kevinr94/Proyecto-Mecatronica-Bogado-Roges/Contenido multimedia/Imagen de WhatsApp 2025-07-23 a las 09.27.17_4d64eca1.jpg

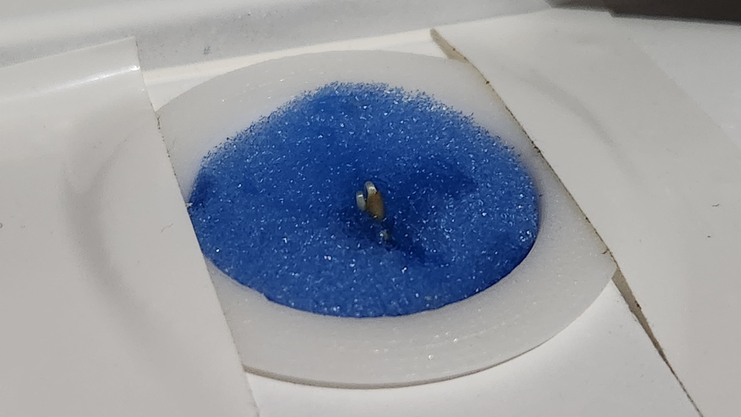
Contenido multimedia/Imagen de WhatsApp 2025-07-23 a las 09.27.17_4d64eca1.jpg
