kevinr94/Proyecto-Mecatronica-Bogado-Roges/Contenido multimedia/Imagen de WhatsApp 2025-07-23 a las 09.27.26_3c1b3ca0.jpg

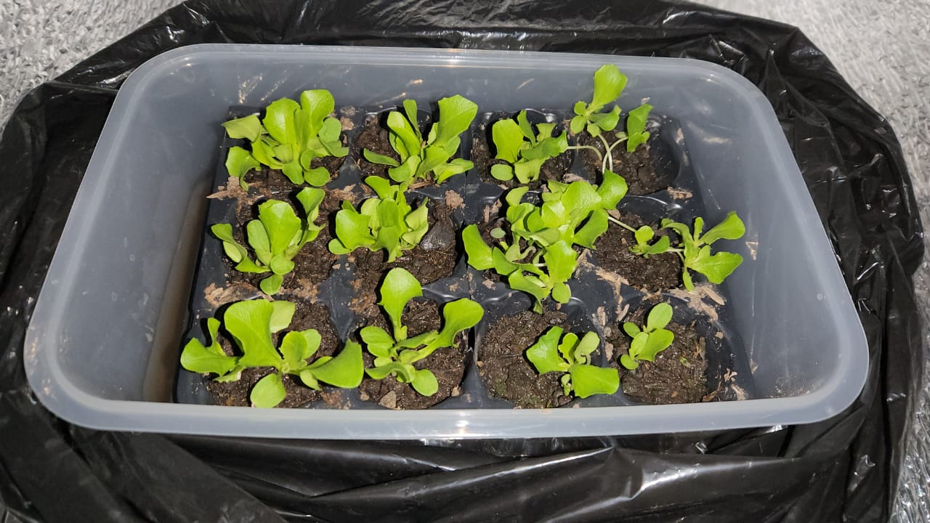
Contenido multimedia/Imagen de WhatsApp 2025-07-23 a las 09.27.26_3c1b3ca0.jpg
