kevinr94/Proyecto-Mecatronica-Bogado-Roges/Contenido multimedia/IMG-20250506-WA0042.jpg

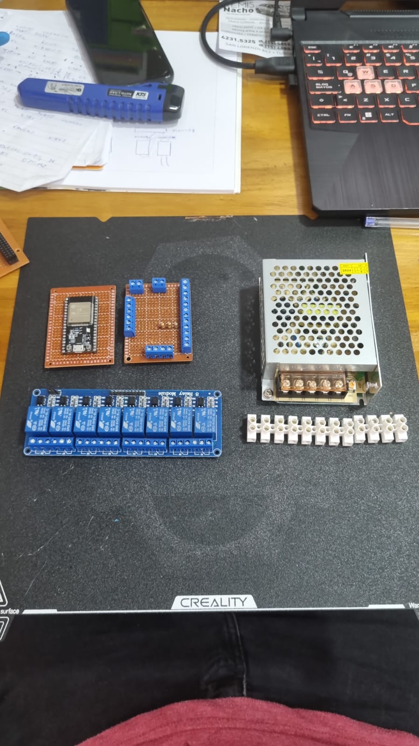
Contenido multimedia/IMG-20250506-WA0042.jpg
