kevinr94/Proyecto-Mecatronica-Bogado-Roges/Contenido multimedia/IMG-20250507-WA0024.jpg

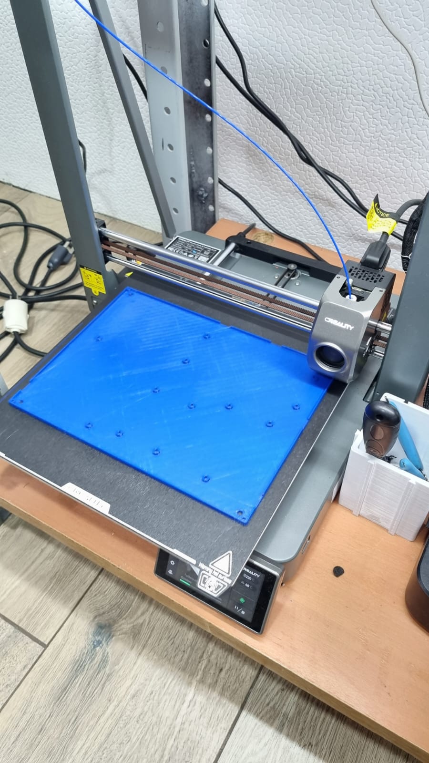
Contenido multimedia/IMG-20250507-WA0024.jpg
