kevinr94/Proyecto-Mecatronica-Bogado-Roges/Contenido multimedia/IMG-20250508-WA0039.jpg

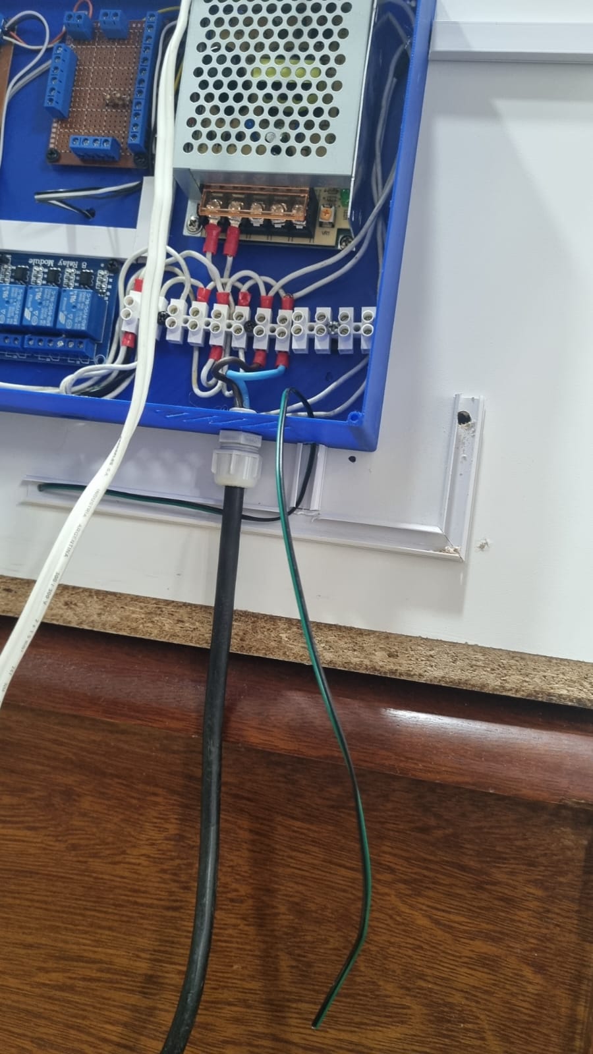
Contenido multimedia/IMG-20250508-WA0039.jpg
