kevinr94/Proyecto-Mecatronica-Bogado-Roges/Contenido multimedia/IMG-20250515-WA0036.jpg

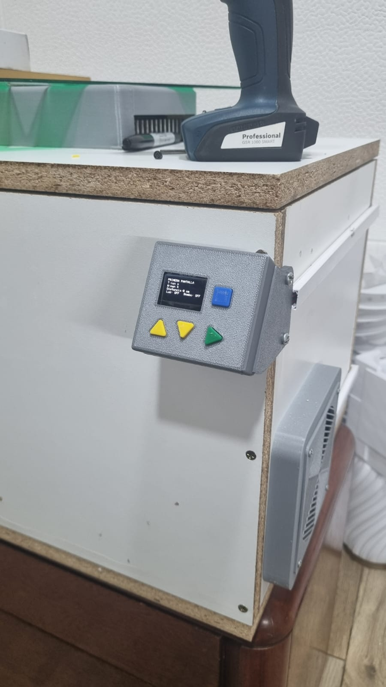
Contenido multimedia/IMG-20250515-WA0036.jpg
