kevinr94/Proyecto-Mecatronica-Bogado-Roges/Contenido multimedia/IMG-20250519-WA0019.jpg

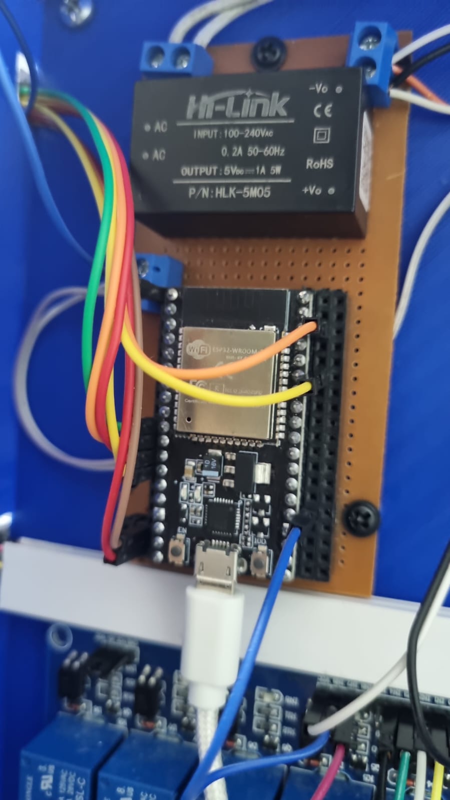
Contenido multimedia/IMG-20250519-WA0019.jpg
