kevinr94/Proyecto-Mecatronica-Bogado-Roges/Contenido multimedia/IMG-20250530-WA0029.jpg

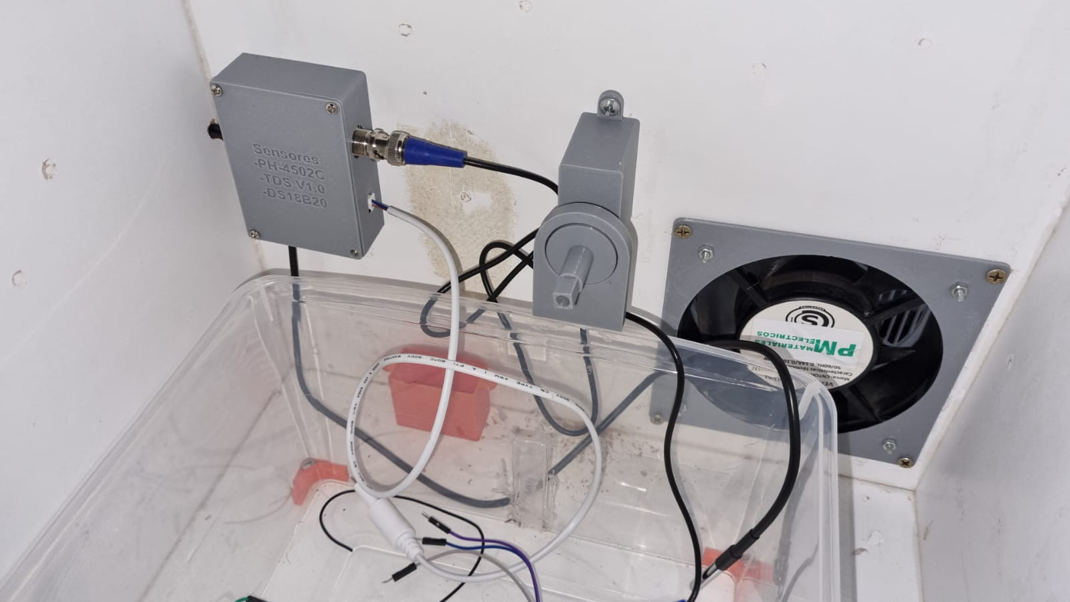
Contenido multimedia/IMG-20250530-WA0029.jpg
