kevinr94/Proyecto-Mecatronica-Bogado-Roges/Contenido multimedia/IMG-20250604-WA0013.jpg

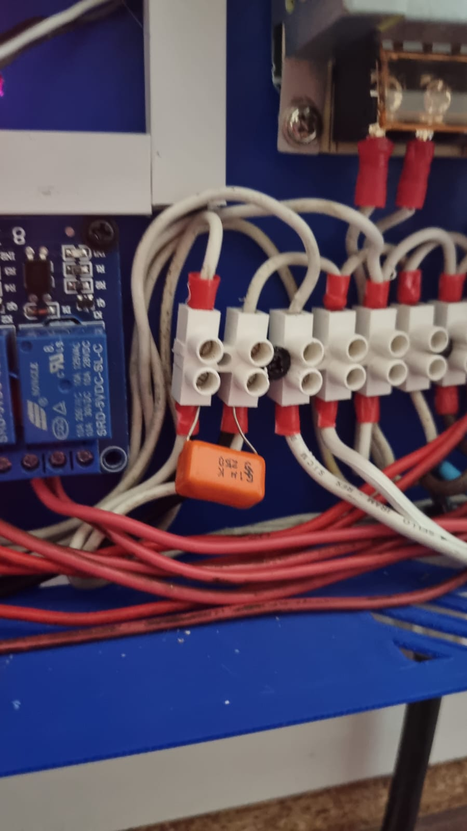
Contenido multimedia/IMG-20250604-WA0013.jpg
