kevinr94/Proyecto-Mecatronica-Bogado-Roges/Contenido multimedia/IMG-20250610-WA0012.jpg

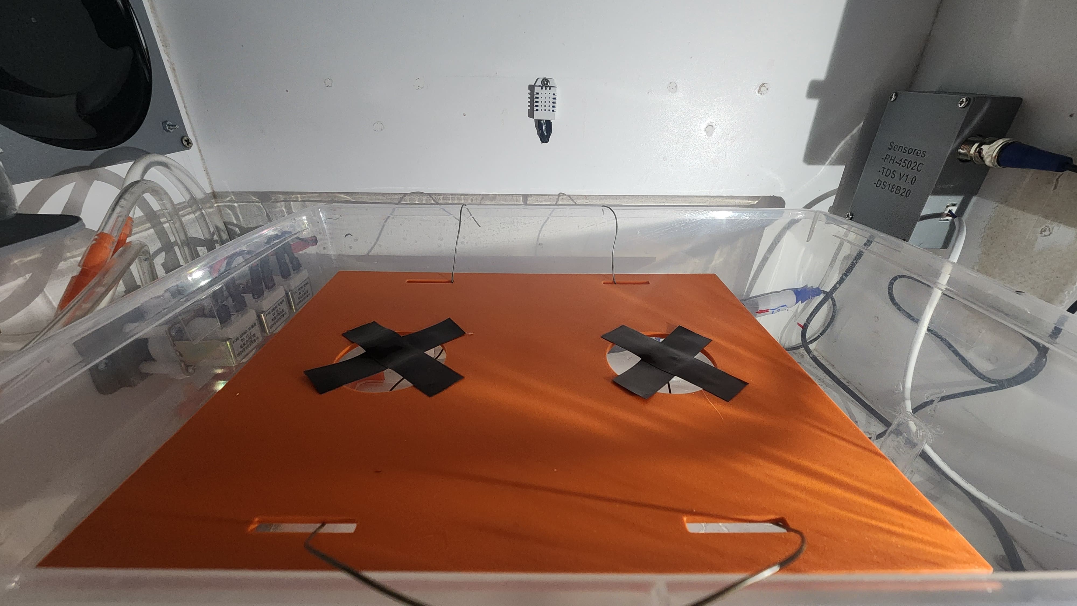
Contenido multimedia/IMG-20250610-WA0012.jpg
