kevinr94/Proyecto-Mecatronica-Bogado-Roges/Contenido multimedia/IMG-20250617-WA0007.jpg

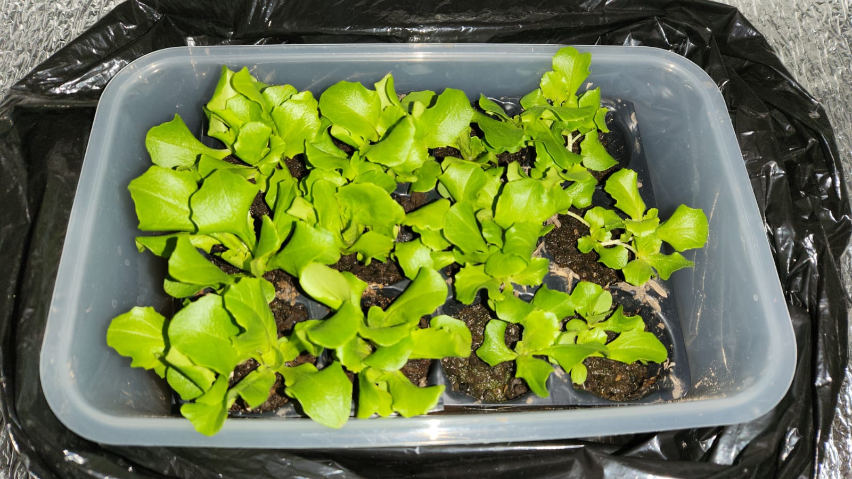
Contenido multimedia/IMG-20250617-WA0007.jpg
