kevinr94/Proyecto-Mecatronica-Bogado-Roges/Contenido multimedia/IMG-20250618-WA0008.jpg

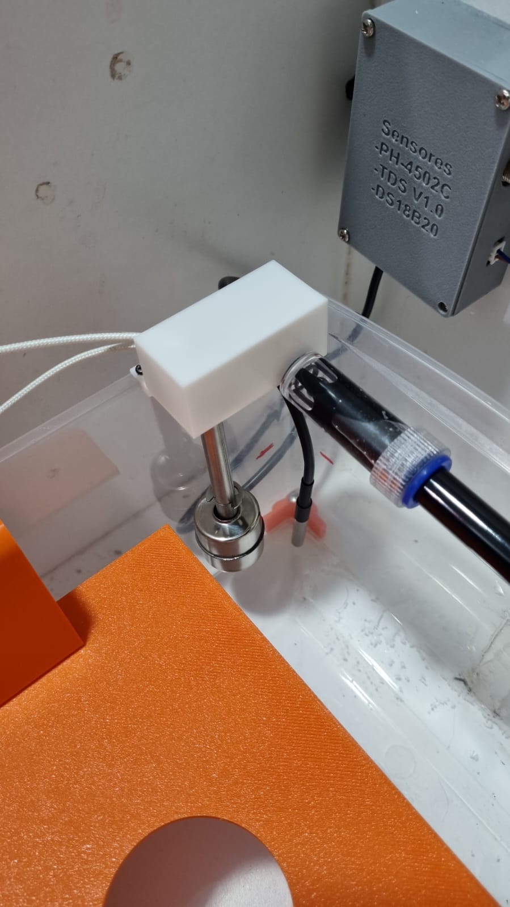
Contenido multimedia/IMG-20250618-WA0008.jpg
