kevinr94/Proyecto-Mecatronica-Bogado-Roges/Contenido multimedia/IMG-20250624-WA0001.jpg

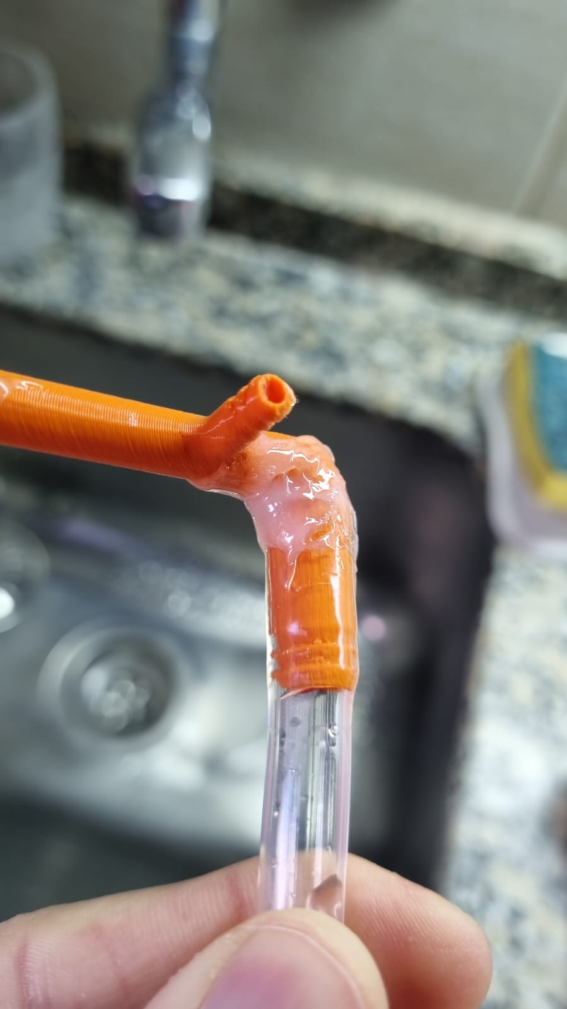
Contenido multimedia/IMG-20250624-WA0001.jpg
