kevinr94/Proyecto-Mecatronica-Bogado-Roges/Contenido multimedia/IMG-20250625-WA0002.jpg

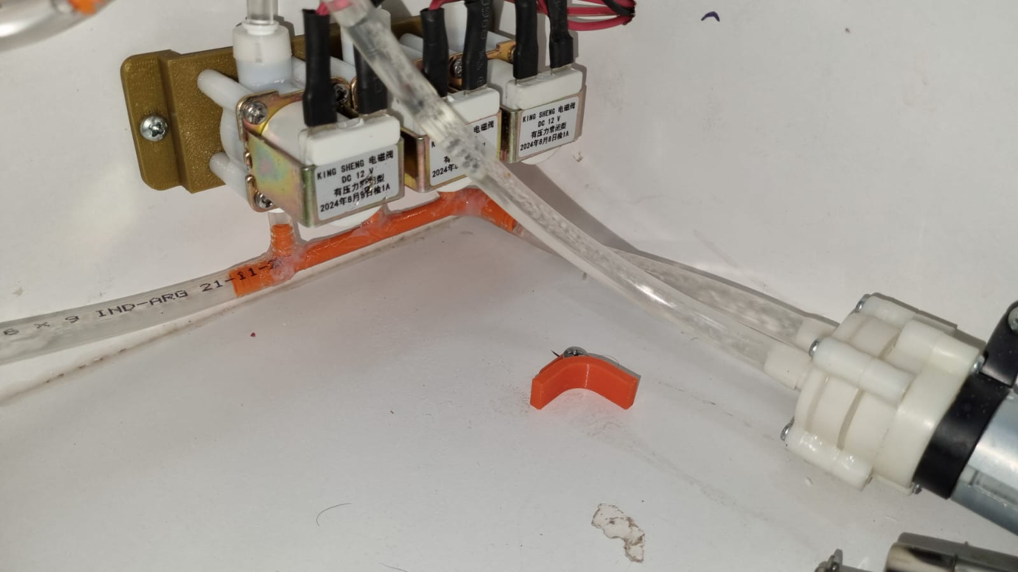
Contenido multimedia/IMG-20250625-WA0002.jpg
