kevinr94/Proyecto-Mecatronica-Bogado-Roges/Contenido multimedia/IMG-20250630-WA0049.jpg

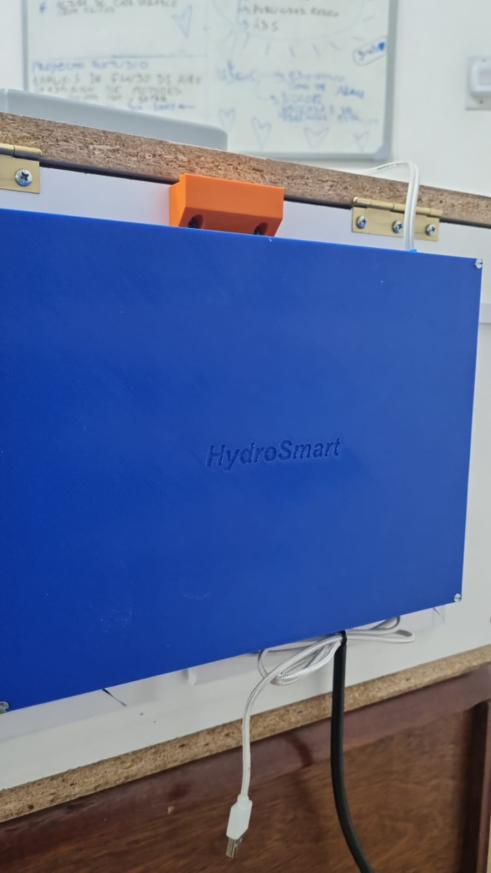
Contenido multimedia/IMG-20250630-WA0049.jpg
