kevinr94/Proyecto-Mecatronica-Bogado-Roges/Contenido multimedia/IMG-20250723-WA0024.jpg

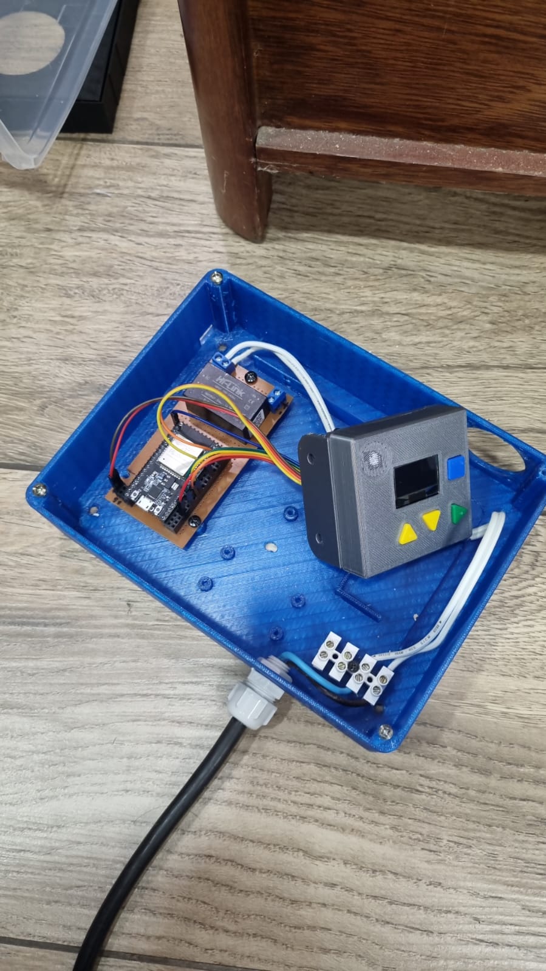
Contenido multimedia/IMG-20250723-WA0024.jpg
