kevinr94/Proyecto-Mecatronica-Bogado-Roges/Contenido multimedia/IMG-20250723-WA0030.jpg

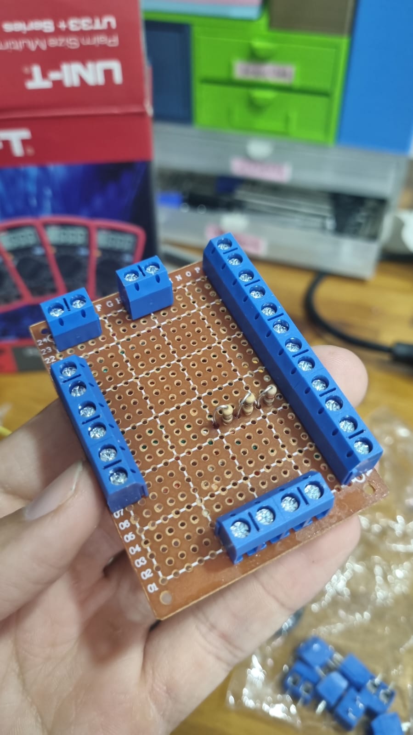
Contenido multimedia/IMG-20250723-WA0030.jpg
