kevinr94/Proyecto-Mecatronica-Bogado-Roges/Archivos 3D para imprimir/Raccord para EV chico.stl

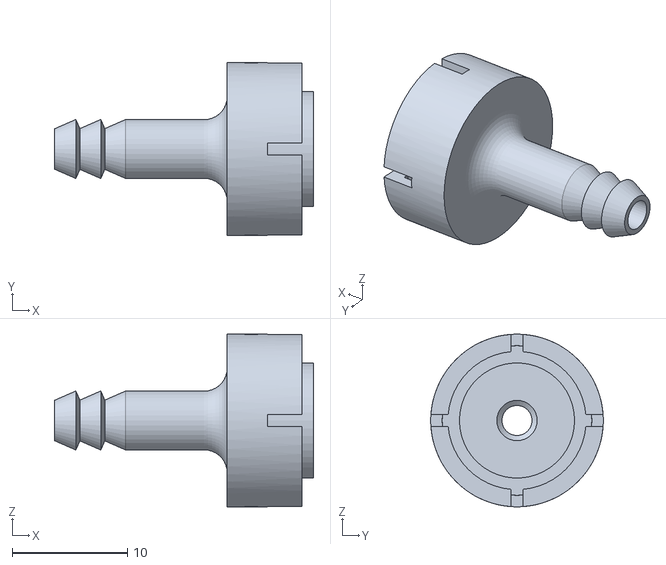
[picture p100: CAD file, 2025-07-23]
Archivos 3D para imprimir/Raccord para EV chico.stl
22.5 x 15.0 x 15.0
