kevinr94/Proyecto-Mecatronica-Bogado-Roges/Archivos 3D para imprimir/Protector iluminacion.stl

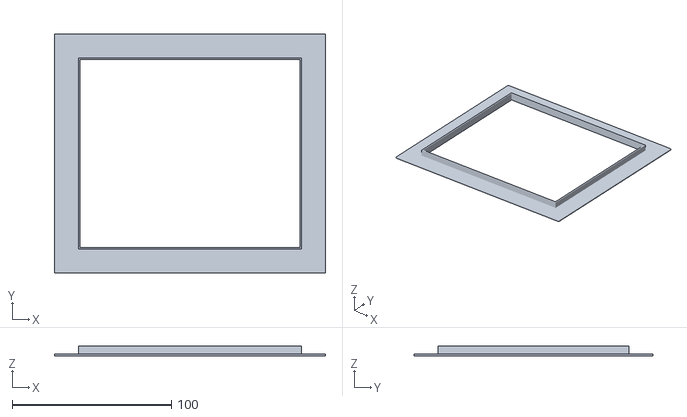
[picture p101: CAD file, 2025-07-23]
Archivos 3D para imprimir/Protector iluminacion.stl
170.0 x 150.0 x 6.00
