kevinr94/Proyecto-Mecatronica-Bogado-Roges/Archivos 3D para imprimir/Soporte electroválvulas.stl

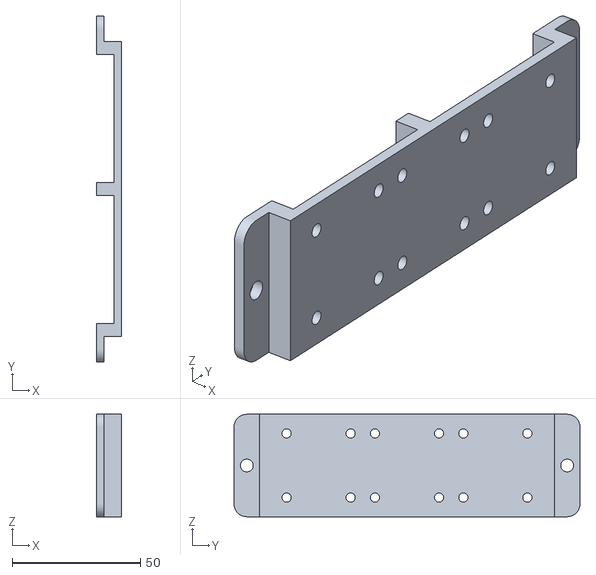
[picture p102: CAD file, 2025-07-23]
Archivos 3D para imprimir/Soporte electroválvulas.stl
9.79 x 135.0 x 40.0
