kevinr94/Proyecto-Mecatronica-Bogado-Roges/Archivos 3D para imprimir/Soporte ultrasonido.stl

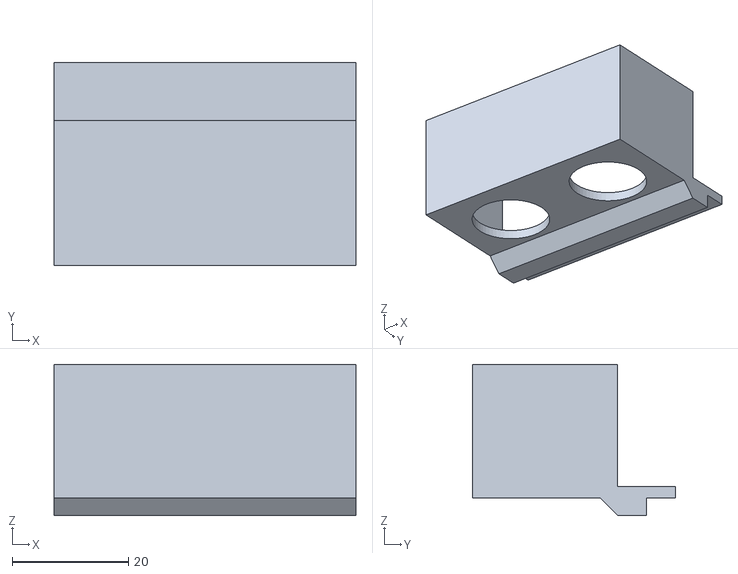
[picture p103: CAD file, 2025-07-23]
Archivos 3D para imprimir/Soporte ultrasonido.stl
52.0 x 35.0 x 26.0
