kevinr94/Proyecto-Mecatronica-Bogado-Roges/Archivos 3D para imprimir/Soporte trasero cooler.stl

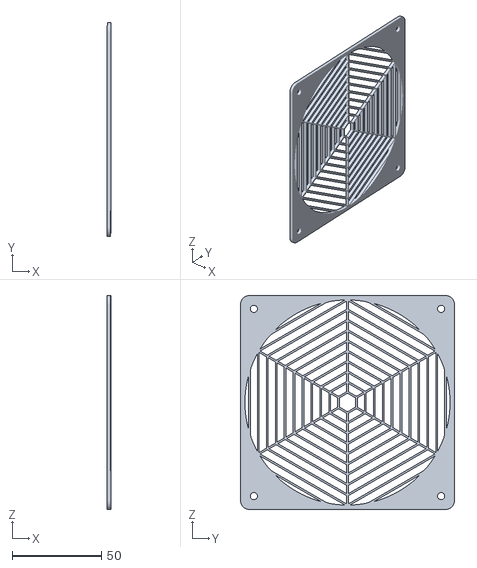
[picture p104: CAD file, 2025-07-23]
Archivos 3D para imprimir/Soporte trasero cooler.stl
2.05 x 120.0 x 120.0
