kevinr94/Proyecto-Mecatronica-Bogado-Roges/Archivos 3D para imprimir/Soporte servomotor.stl

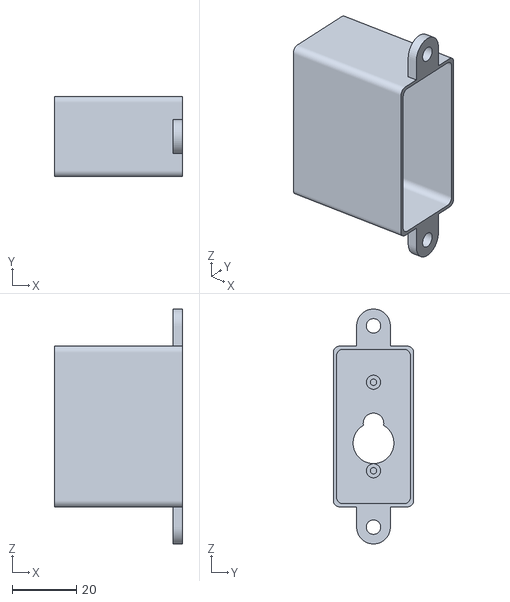
[picture p105: CAD file, 2025-07-23]
Archivos 3D para imprimir/Soporte servomotor.stl
39.9 x 25.0 x 73.1
