kevinr94/Proyecto-Mecatronica-Bogado-Roges/Archivos 3D para imprimir/Soporte fan iluminacion.stl

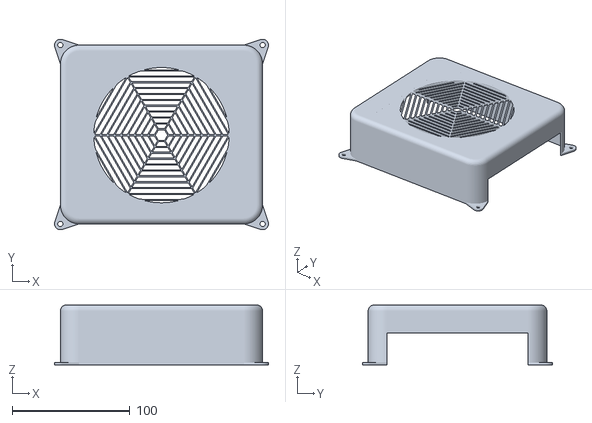
[picture p106: CAD file, 2025-07-23]
Archivos 3D para imprimir/Soporte fan iluminacion.stl
182.0 x 162.0 x 51.0
