kevinr94/Proyecto-Mecatronica-Bogado-Roges/Archivos 3D para imprimir/Tablero electrico.stl

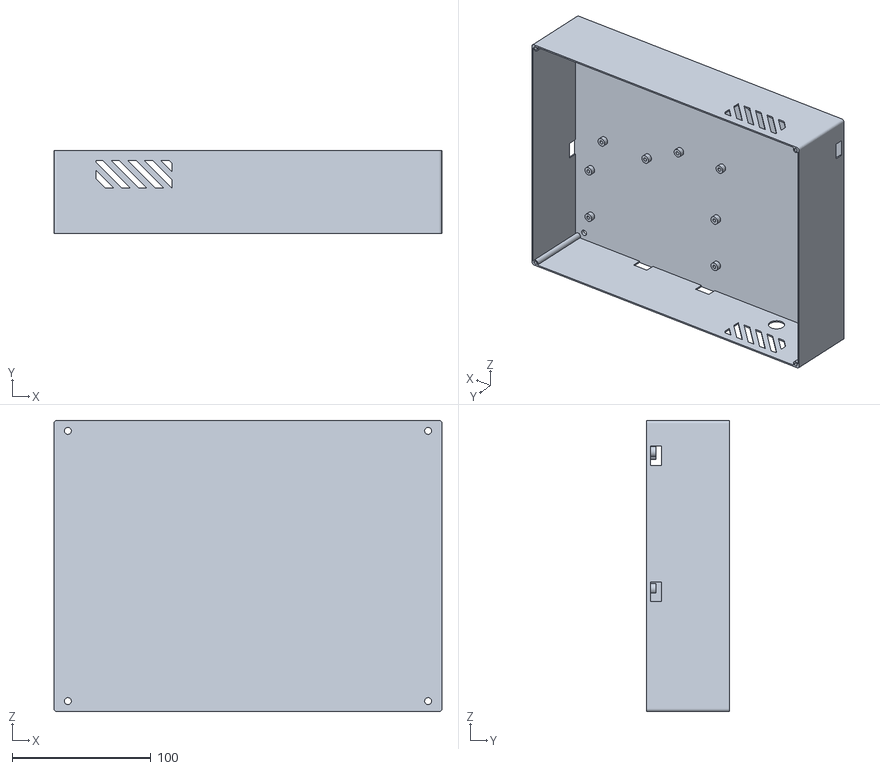
[picture p107: CAD file, 2025-07-23]
Archivos 3D para imprimir/Tablero electrico.stl
280.0 x 60.0 x 210.0
