kevinr94/Proyecto-Mecatronica-Bogado-Roges/Archivos 3D para imprimir/Carcasa base.stl

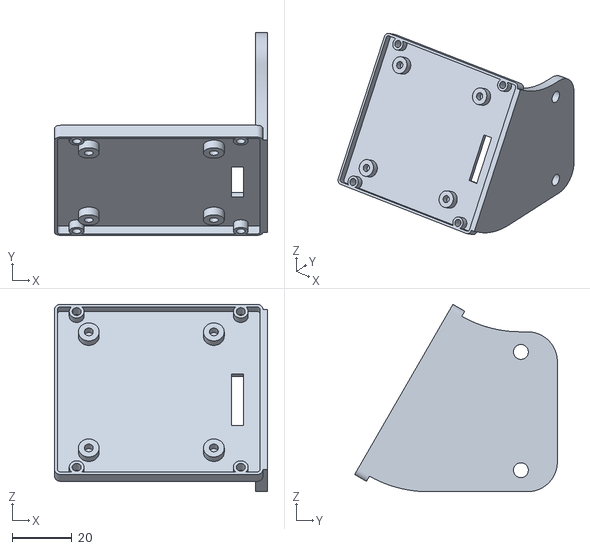
[picture p108: CAD file, 2025-07-23]
Archivos 3D para imprimir/Carcasa base.stl
71.5 x 68.1 x 62.9
