kevinr94/Proyecto-Mecatronica-Bogado-Roges/Archivos 3D para imprimir/Reparacion EV.stl

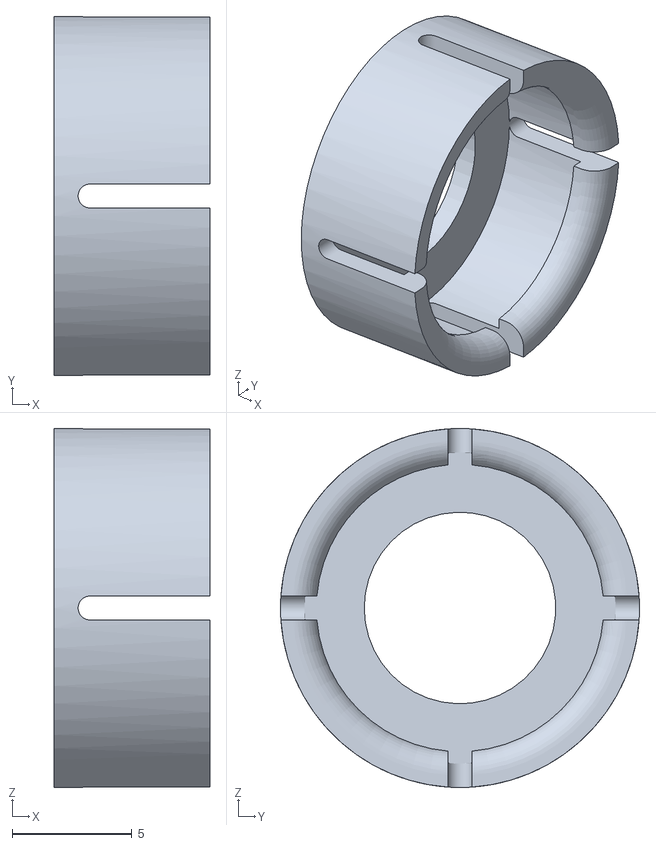
[picture p109: CAD file, 2025-07-23]
Archivos 3D para imprimir/Reparacion EV.stl
6.50 x 15.0 x 15.0
