kevinr94/Proyecto-Mecatronica-Bogado-Roges/Archivos 3D para imprimir/racor.stl

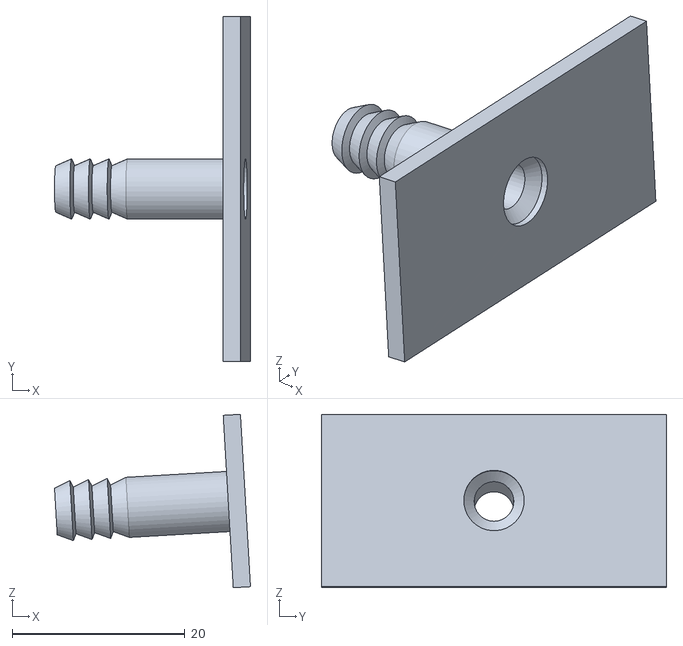
[picture p110: CAD file, 2025-07-23]
Archivos 3D para imprimir/racor.stl
22.7 x 40.0 x 20.1
