kevinr94/Proyecto-Mecatronica-Bogado-Roges/Archivos 3D para imprimir/Soportes sensore.stl

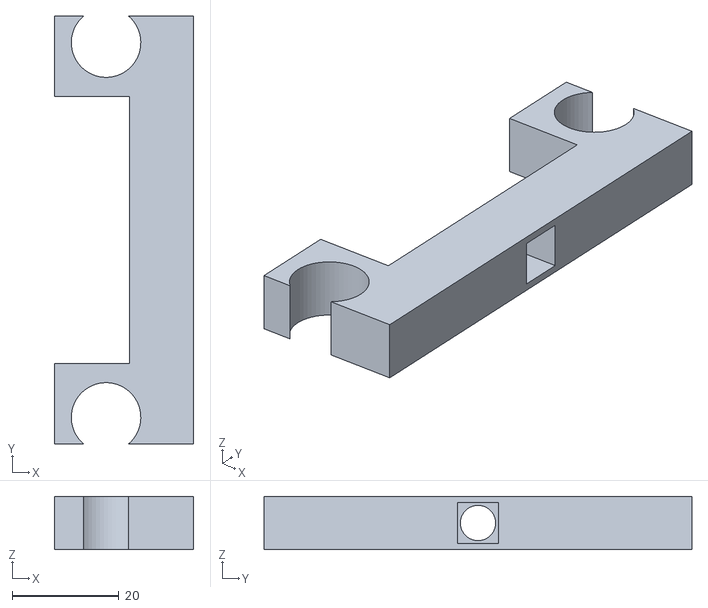
[picture p111: CAD file, 2025-07-23]
Archivos 3D para imprimir/Soportes sensore.stl
26.0 x 80.0 x 10.0
