kevinr94/Proyecto-Mecatronica-Bogado-Roges/Archivos 3D para imprimir/Soporte cooler.stl

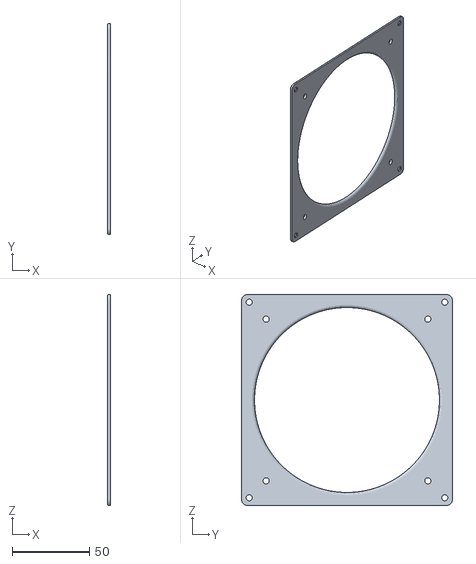
[picture p112: CAD file, 2025-07-23]
Archivos 3D para imprimir/Soporte cooler.stl
2.05 x 137.0 x 137.0
