kevinr94/Proyecto-Mecatronica-Bogado-Roges/Archivos 3D para imprimir/Soprote betea.stl

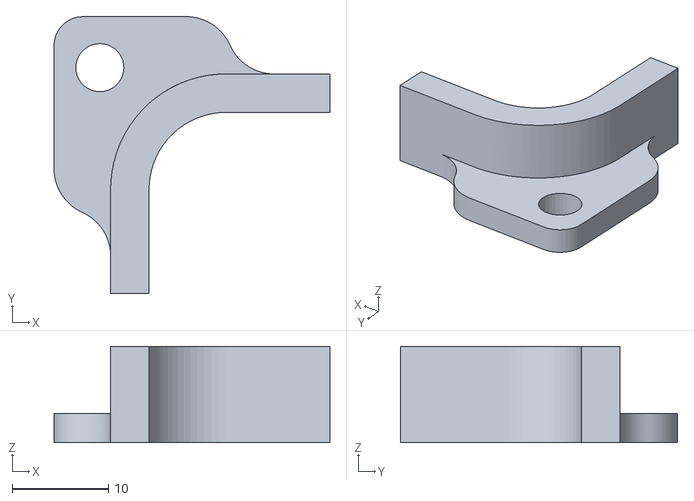
[picture p113: CAD file, 2025-07-23]
Archivos 3D para imprimir/Soprote betea.stl
28.7 x 28.8 x 10.0
