kevinr94/Proyecto-Mecatronica-Bogado-Roges/Archivos 3D para imprimir/Eje servomotor.stl

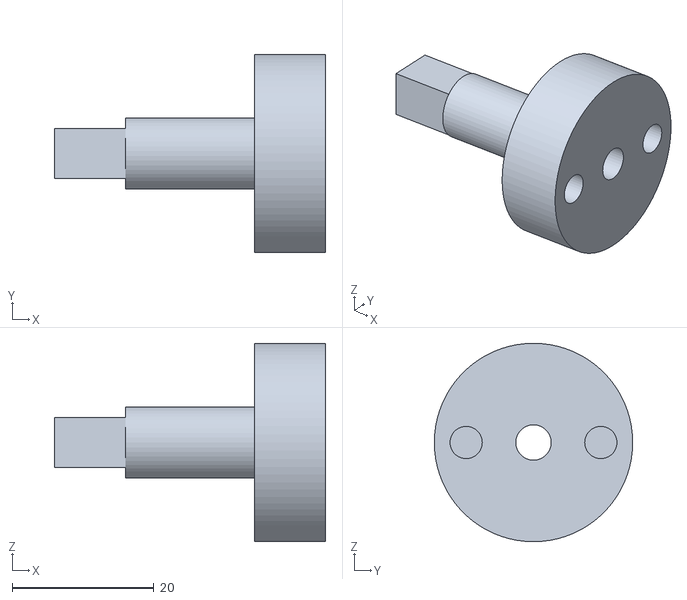
[picture p114: CAD file, 2025-07-23]
Archivos 3D para imprimir/Eje servomotor.stl
38.2 x 28.0 x 28.0
