kevinr94/Proyecto-Mecatronica-Bogado-Roges/Archivos 3D para imprimir/Carcasa.stl

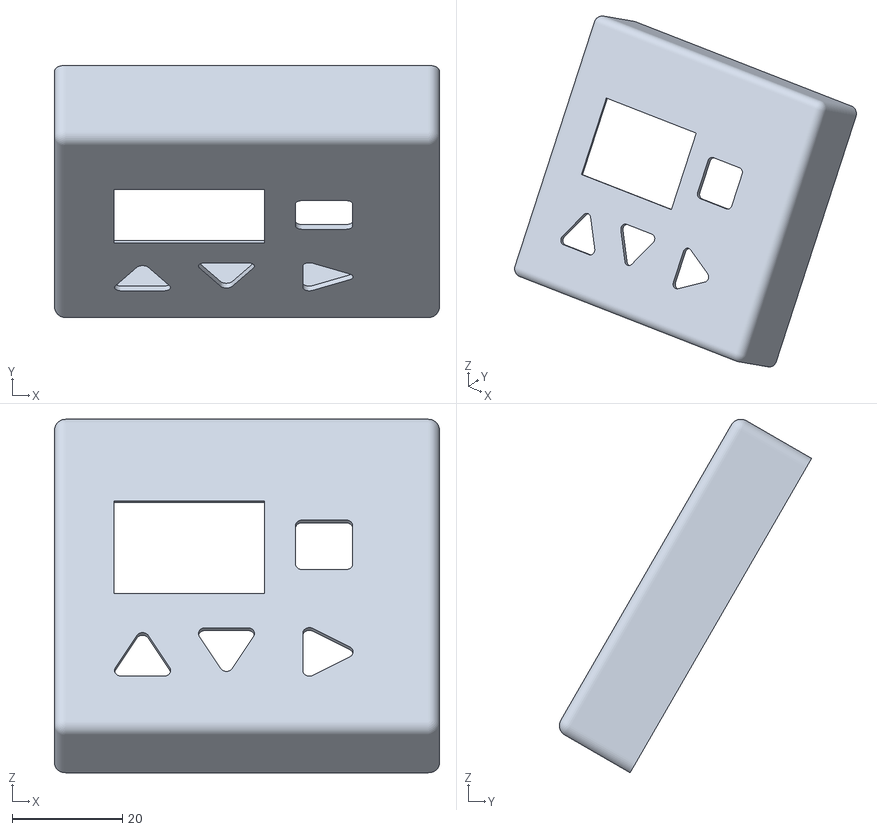
[picture p115: CAD file, 2025-07-23]
Archivos 3D para imprimir/Carcasa.stl
70.0 x 45.9 x 64.3
