kevinr94/Proyecto-Mecatronica-Bogado-Roges/Archivos 3D para imprimir/Adaptador tablero.stl

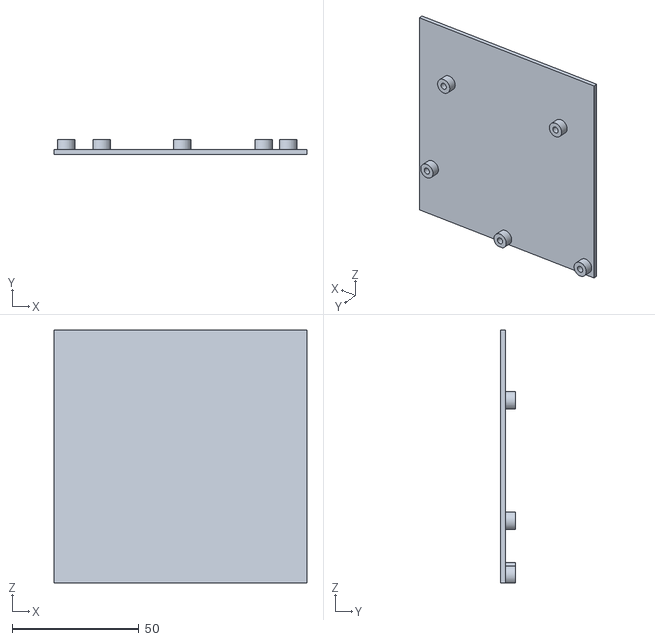
[picture p116: CAD file, 2025-07-23]
Archivos 3D para imprimir/Adaptador tablero.stl
100.0 x 6.00 x 100.0
